ellak-monades-aristeias/The_Wi-Fi_seat/images/wi-fi_seat_night.pdf

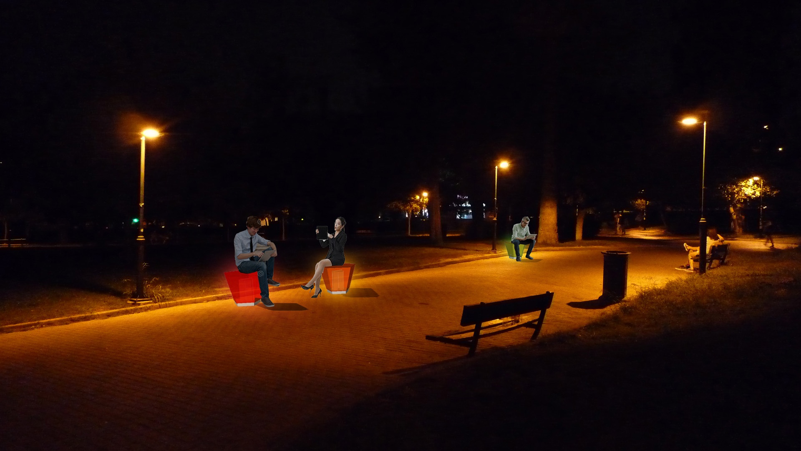
[picture p9: page 1]
