ellak-monades-aristeias/The_Wi-Fi_seat/dxf/base_complete.jpg

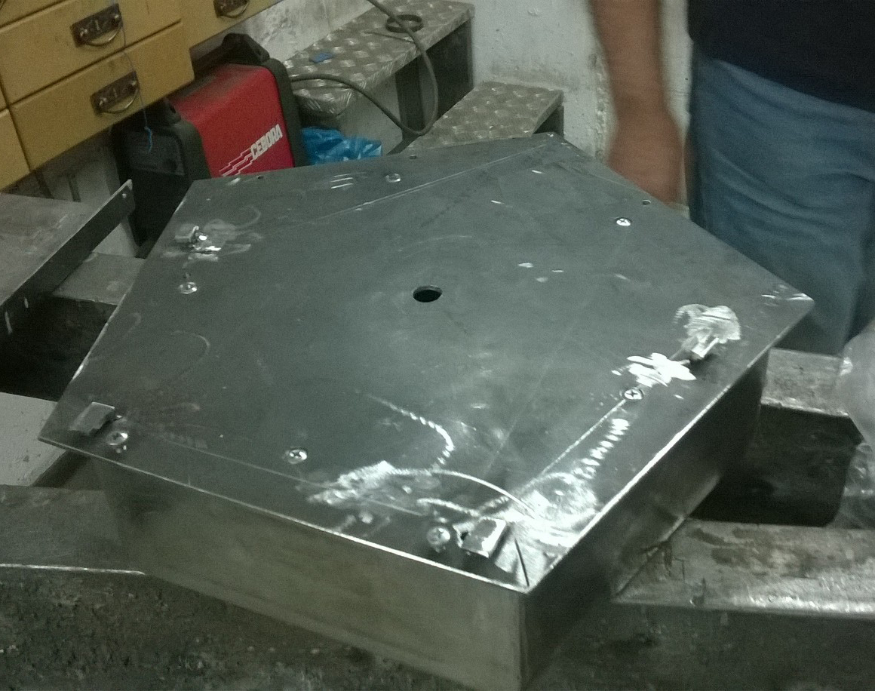
dxf/base_complete.jpg
