ellak-monades-aristeias/The_Wi-Fi_seat/dxf/box.jpg

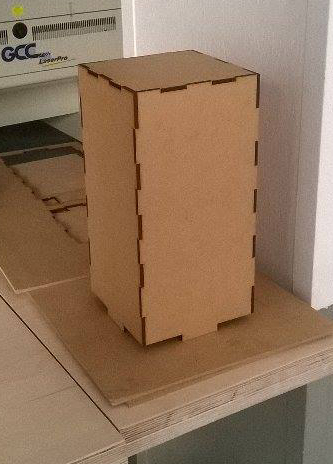
dxf/box.jpg
