ellak-monades-aristeias/The_Wi-Fi_seat/dxf/plexiglass.jpg

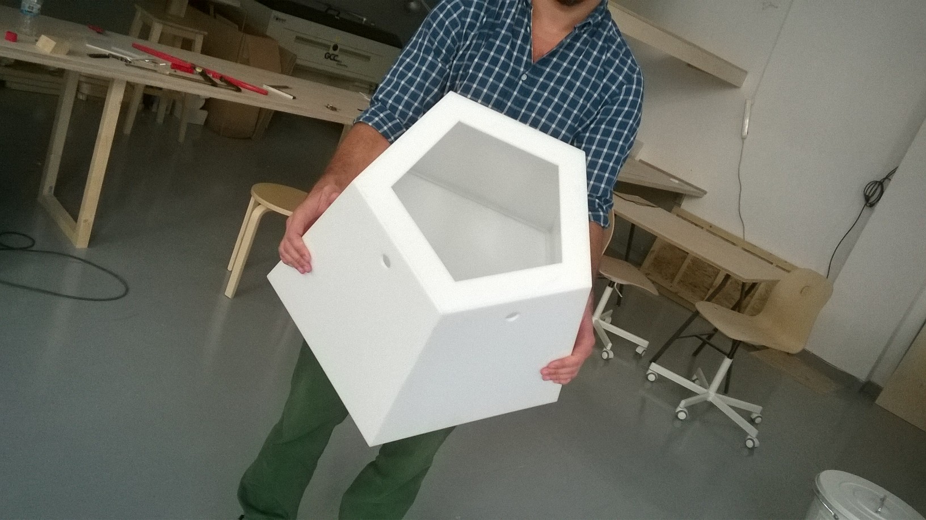
dxf/plexiglass.jpg
