ellak-monades-aristeias/The_Wi-Fi_seat/images/signal_1.jpg

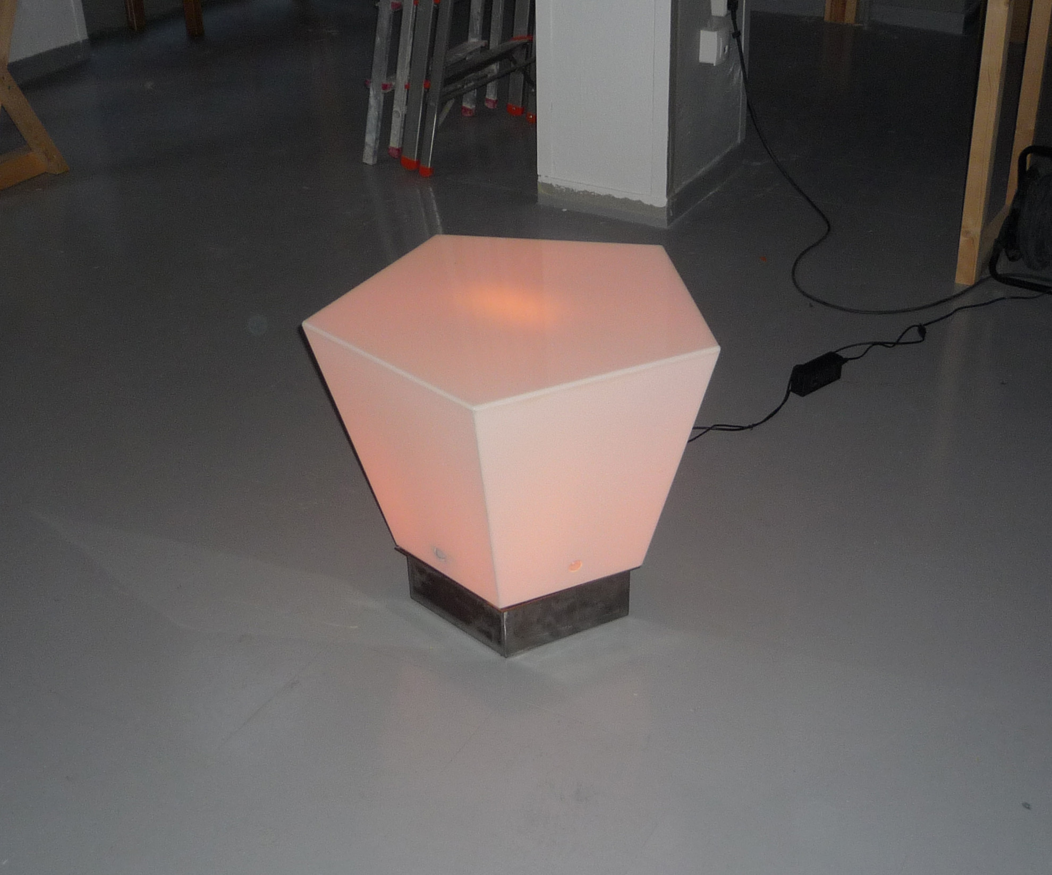
images/signal_1.jpg
